IeiuniumLux/PetPy/img/image1.png

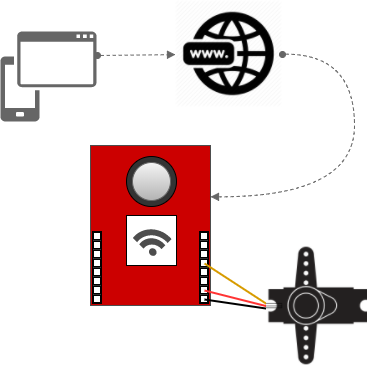
img/image1.png
