IeiuniumLux/PetPy/img/image2.png

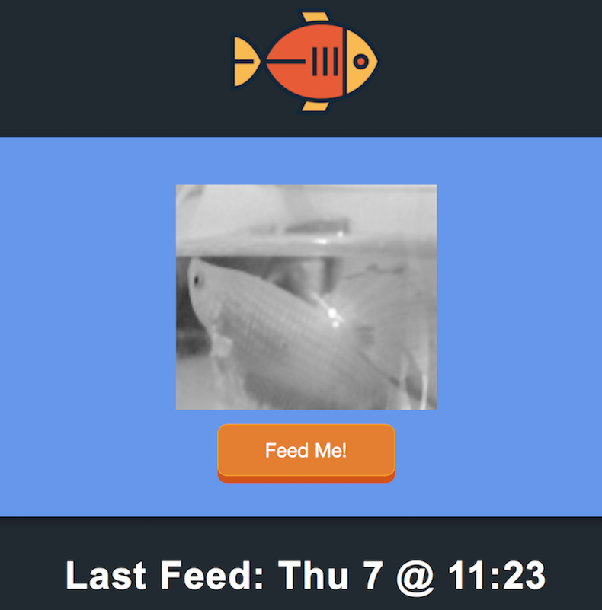
img/image2.png
